mhorimoto/M302/M302-3d01.png

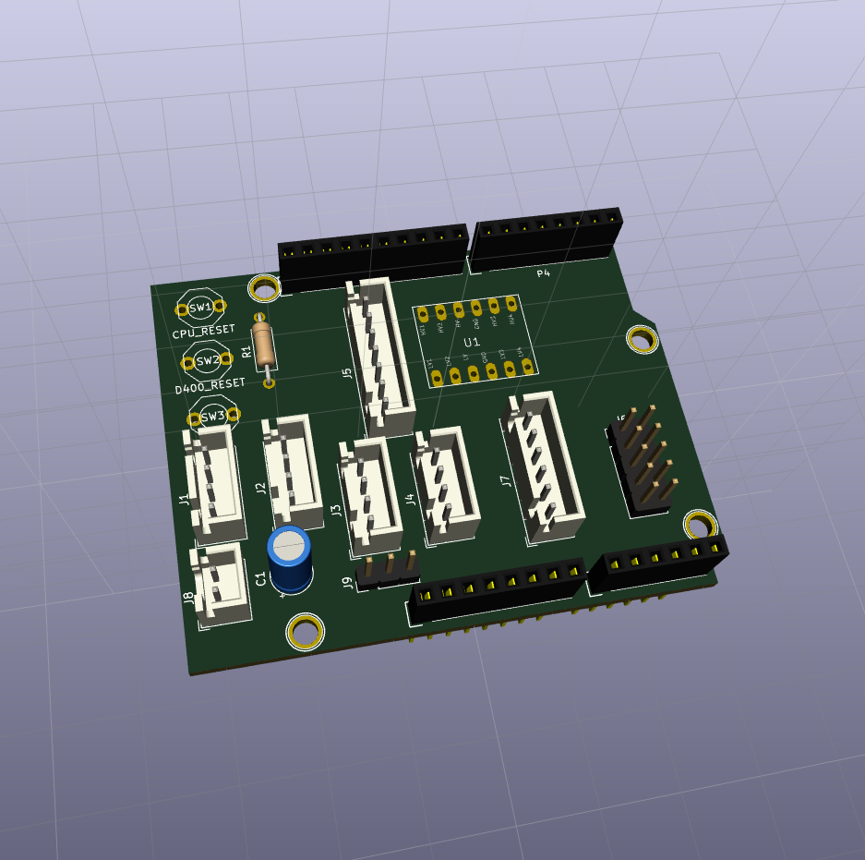
M302-3d01.png
