mhorimoto/M302/M302-3d03.png

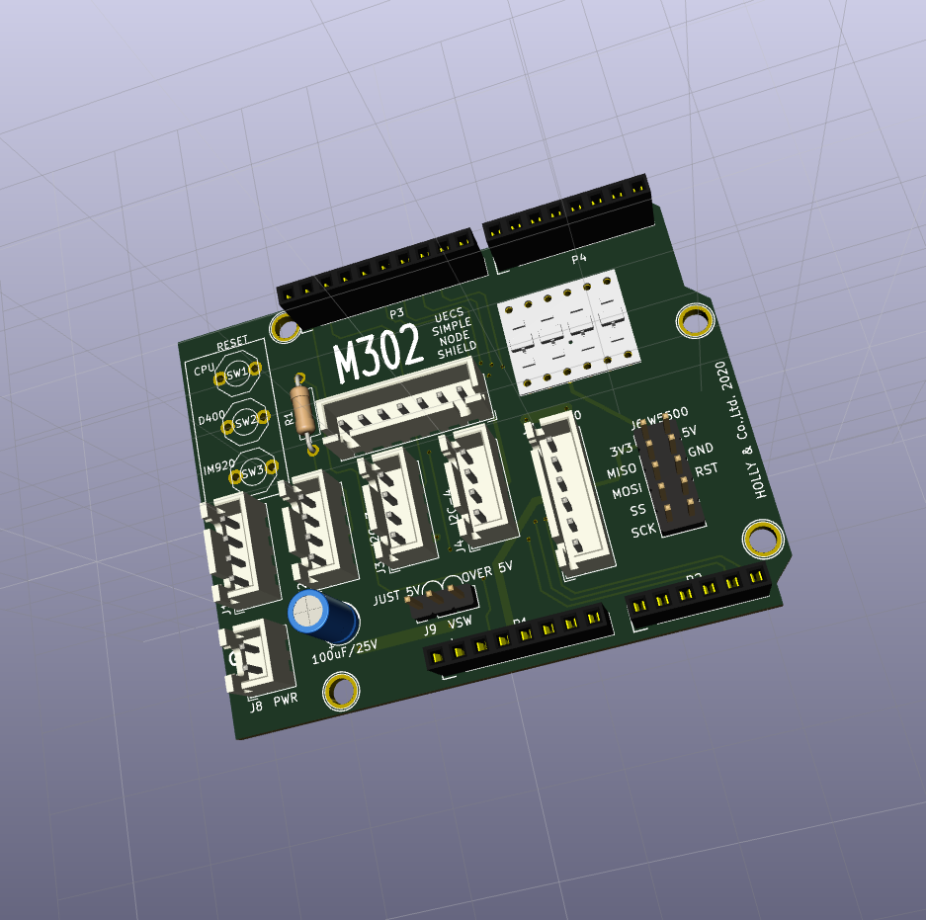
M302-3d03.png
