mhorimoto/M302/M302-3d04.png

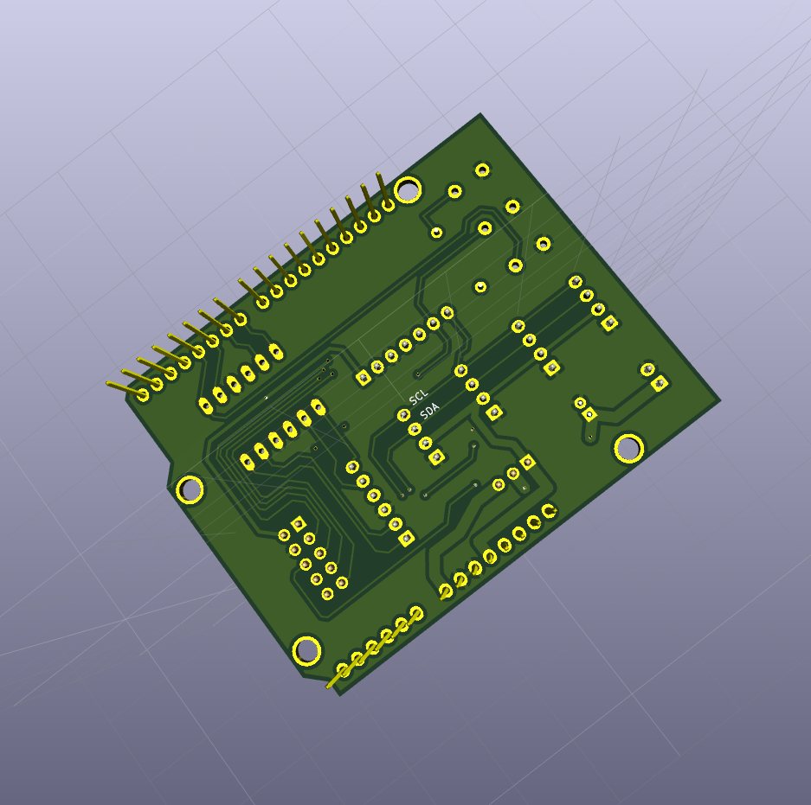
M302-3d04.png
