mhorimoto/M302/M302-3d05.png

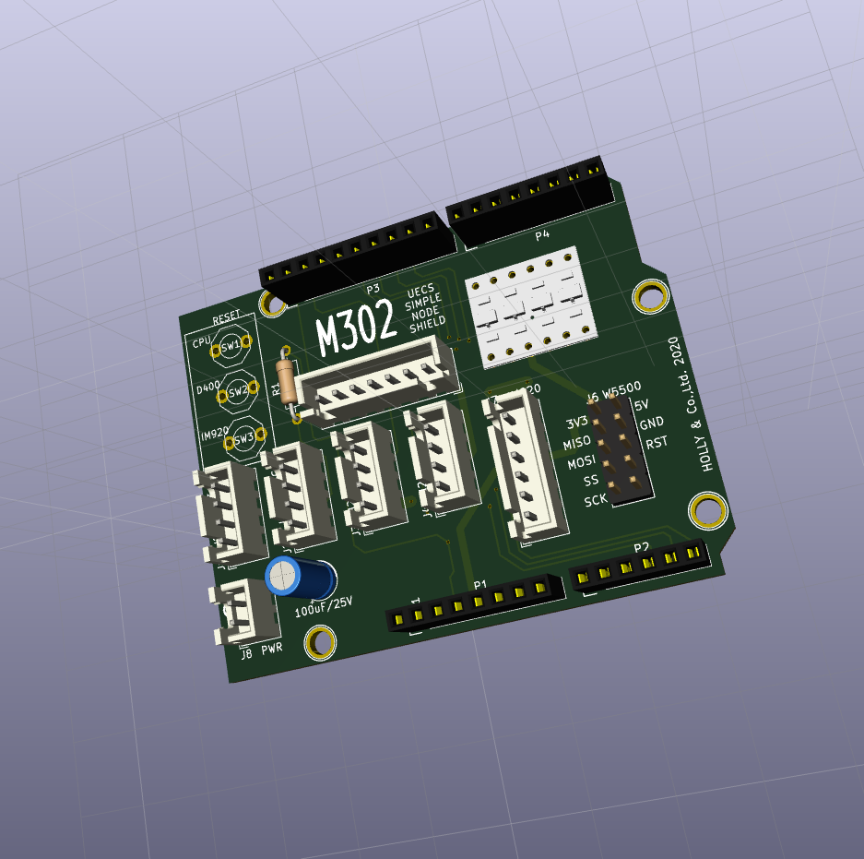
M302-3d05.png
